tomonoriyamazaki/toytalk/web/tanuki_idle.png

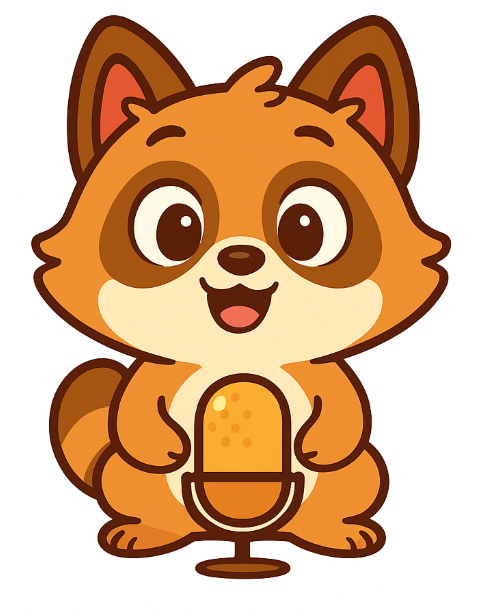
web/tanuki_idle.png
