tomonoriyamazaki/toytalk/devices/KiCad/OPL_Kicad_Library-master/OPL_Kicad_Library-master/Seeed Studio Wio SX1262 for XIAO nRF52840 v1.3/Wio-SX1262 for XIAO nRF52840.kicad_pcb

## KiCad design devices/KiCad/OPL_Kicad_Library-master/OPL_Kicad_Library-master/Seeed Studio Wio SX1262 for XIAO nRF52840 v1.3/Wio-SX1262 for XIAO nRF52840.kicad_pcb (2026-01-03)


Parts:
C1: 100nF; C0402; Voltage Rating 16V,X7R; MPN CC0402KRX7R7BB104
J1, J2: Header 1x7 2.54mm; H7-2.54; Part Type Header
K1: TS-1188E 6C81; SW4-SMD-7.0X3.5X3.5MM-90D; MPN TS-1188E 6C81; not fitted
R1: 10K; R0402; Power Rating 5%; MPN RC0402JR-0710KL
R2: 10K; R0402; Power Rating 5%; MPN RC0402JR-0710KL; not fitted
R3, R4, R5, R6: 22R; R0402; Power Rating 1%; MPN RC0402FR-0722RL
U1: Wio-SX1262; MODULE12P-1.27-11X11.6MM; MPN Wio-SX1262

Connections:
+3V3: C1.1, J2.3, R1.2, R2.2, U1.8 (VCC)
/D0: J1.1, K1.2, R2.1
/LORA_BUSY: J1.4, U1.11 (BUSY)
/LORA_DIO1: J1.2, U1.12 (DIO1)
/LORA_RF_SW1: J1.6, U1.1 (RF_SW1)
/LORA_RST: J1.3, R1.1, U1.5 (RST)
/LORA_SPI_MISO: J2.5, R4.1
/LORA_SPI_MOSI: J2.4, R5.1
/LORA_SPI_NSS: J1.5, R3.1
/LORA_SPI_SCK: J2.6, R6.1
GND: C1.2, J2.2, K1.1, K1.3 (S1), K1.4 (S2), U1.7 (GND1), U1.10 (GND2)
unnamed: R4.2, U1.2 (MISO)
unnamed: R5.2, U1.3 (MOSI)
unnamed: R3.2, U1.6 (NSS)
unnamed: R6.2, U1.4 (SCK)
VIN: J2.1


Board: 2 copper layers, 17.8 x 21.4 mm, 11 parts (0 on the bottom side), 15 nets.
