tomonoriyamazaki/toytalk/devices/mcu/esp32_s3/audio_speaker_tts_3/audio_speaker_tts_3.ino

#include <WiFi.h>
#include <WiFiClientSecure.h>
#include <driver/i2s.h>
#include "mbedtls/base64.h"

// ==== WiFi ====
const char* WIFI_SSID = "Buffalo-G-5830";
const char* WIFI_PASS = "sh6s3kagpp48s";

// ==== Lambda ====
const char* LAMBDA_HOST = "hbik6fueesqaftzkehtbwrr2ra0ucusi.lambda-url.ap-northeast-1.on.aws";
const char* LAMBDA_PATH = "/";

// ==== I2S PIN ====
#define PIN_BCLK   4
#define PIN_LRC    3
#define PIN_DOUT   5
#define PIN_AMP_SD 6

// ===== 追加: 受信状態 =====
String curEvent = "";
int curId = -1;
String curB64 = "";
bool inTtsJson = false;

// ===== mono → stereo 変換（音量調整付き） =====
void monoToStereo(int16_t* mono, int16_t* stereo, size_t samples) {
  const float VOLUME = 0.3;  // 30%に減衰（0.0-1.0）GAINピン未接続対策

  for (size_t i = 0; i < samples; i++) {
    int16_t sample = (int16_t)(mono[i] * VOLUME);
    stereo[2*i]     = sample;
    stereo[2*i + 1] = sample;
  }
}

// ===== 追加: イベント終了処理 =====
void handleEventEnd() {
  if (curEvent == "tts" && curId >= 0 && curB64.length() > 0) {
    Serial.println("===== COMPLETE PCM =====");
    Serial.printf("id=%d, b64_len=%d\n", curId, curB64.length());

    // Base64デコード（PSRAMを使用）
    size_t out_len = 0;
    int maxOut = curB64.length();
    uint8_t* mono_pcm = (uint8_t*)ps_malloc(maxOut);  // malloc → ps_malloc

    if (!mono_pcm) {
      Serial.println("[ERR] ps_malloc failed");
      curEvent = "";
      curId = -1;
      curB64 = "";
      inTtsJson = false;
      return;
    }

    int ret = mbedtls_base64_decode(
      mono_pcm, maxOut, &out_len,
      (const unsigned char*)curB64.c_str(),
      curB64.length()
    );

    Serial.printf("[DECODE] ret=%d, out_len=%d\n", ret, out_len);

    if (ret != 0 || out_len == 0) {
      Serial.println("[ERR] decode failed");
      free(mono_pcm);
      curEvent = "";
      curId = -1;
      curB64 = "";
      inTtsJson = false;
      return;
    }

    // mono → stereo 変換（PSRAMを使用）
    size_t samples = out_len / 2;
    size_t stereo_bytes = samples * 4;
    int16_t* stereo = (int16_t*)ps_malloc(stereo_bytes);  // malloc → ps_malloc

    if (!stereo) {
      Serial.println("[ERR] stereo ps_malloc failed");
      free(mono_pcm);
      curEvent = "";
      curId = -1;
      curB64 = "";
      inTtsJson = false;
      return;
    }

    monoToStereo((int16_t*)mono_pcm, stereo, samples);

    // I2S 再生
    size_t written = 0;
    i2s_write(I2S_NUM_1, stereo, stereo_bytes, &written, portMAX_DELAY);
    Serial.printf("[I2S] written=%d bytes\n", written);

    free(stereo);
    free(mono_pcm);
    Serial.println("========================");
  }

  curEvent = "";
  curId = -1;
  curB64 = "";
  inTtsJson = false;
}


// ===== 追加: 行ごとの処理 =====
void processLine(String line) {
  line.trim();

  // ---- chunk-size(hex) 行スキップ ----
  bool isHex = true;
  if (line.length() > 0) {
    for (int i = 0; i < line.length(); i++) {
      if (!isxdigit(line[i])) { isHex = false; break; }
    }
  }
  if (isHex && line.length() <= 4) {
    return;
  }

  // ---- event: ----
  if (line.startsWith("event:")) {
    // handleEventEnd();   // ← ①削除（ここだけ変更）
    curEvent = line.substring(6);
    curEvent.trim();
    return;
  }

  // ---- data: 最初の JSON ----
  if (line.startsWith("data:")) {
    String d = line.substring(5);
    d.trim();

    if (curEvent == "tts" && d.startsWith("{")) {
      // id
      int p = d.indexOf("\"id\":");
      if (p >= 0) {
        p += 5;
        int e = p;
        while (e < d.length() && isdigit(d[e])) e++;
        curId = d.substring(p, e).toInt();
      }

      // b64（途中のため " が無い場合あり）
      int b = d.indexOf("\"b64\":\"");
      if (b >= 0) {
        b += 7;
        String part = d.substring(b);
        part.replace("\"", "");
        curB64 += part;
      }

      inTtsJson = true;
    }
    return;
  }

  // ---- TTS JSON の途中チャンク ----
  if (curEvent == "tts" && inTtsJson) {

    // 終端 "}" チェック
    if (line.endsWith("\"}")) {
      String tmp = line;
      tmp.replace("\"}", "");
      curB64 += tmp;
      handleEventEnd();
      return;
    }

    // base64 続き
    curB64 += line;
    return;
  }

  // 他の行は無視
}


// ==== Lambda に固定メッセージ送って SSE を処理 ====
void sendSimpleSSE(const String& text)
{
  Serial.println("🚀 Sending to Lambda: " + text);

  WiFiClientSecure client;
  client.setInsecure();

  if (!client.connect(LAMBDA_HOST, 443)) {
    Serial.println("❌ connect failed");
    return;
  }

  // 送信ペイロード
  String payload =
    "{\"model\":\"OpenAI\",\"voice\":\"nova\","
    "\"messages\":[{\"role\":\"user\",\"content\":\"" + text + "\"}]}";

  // HTTPリクエスト
  String req =
    String("POST ") + LAMBDA_PATH + " HTTP/1.1\r\n"
    "Host: " + LAMBDA_HOST + "\r\n"
    "Content-Type: application/json\r\n"
    "Accept: text/event-stream\r\n"
    "Connection: close\r\n"
    "Content-Length: " + payload.length() + "\r\n\r\n"
    + payload;

  client.print(req);

  Serial.println("📡 Waiting SSE header...");

  // ---- HTTPヘッダ飛ばす ----
  while (true) {
    String line = client.readStringUntil('\n');
    if (line.length() == 0 || line == "\r") break;
  }

  Serial.println("📨 SSE START --------------------------------");

  // ---- SSEボディ ----
  while (client.connected() || client.available()) {
    if (client.available()) {
      String line = client.readStringUntil('\n');
      Serial.print("[RAW] ");
      Serial.println(line);
      processLine(line);   // ★追加
    } else {
      delay(1);
    }
  }

  Serial.println("🏁 SSE END ----------------------------------");

  handleEventEnd();  // 念のため
}

// ==== I2S セットアップ ====
void setupI2S() {
  pinMode(PIN_AMP_SD, OUTPUT);
  digitalWrite(PIN_AMP_SD, HIGH);

  i2s_config_t cfg = {
    .mode = (i2s_mode_t)(I2S_MODE_MASTER | I2S_MODE_TX),
    .sample_rate = 24000,
    .bits_per_sample = I2S_BITS_PER_SAMPLE_16BIT,
    .channel_format = I2S_CHANNEL_FMT_RIGHT_LEFT,
    .communication_format = (i2s_comm_format_t)(I2S_COMM_FORMAT_I2S | I2S_COMM_FORMAT_I2S_MSB),
    .intr_alloc_flags = 0,
    .dma_buf_count = 8,
    .dma_buf_len = 1024,
    .use_apll = true,
    .tx_desc_auto_clear = true,
    .fixed_mclk = 0
  };

  i2s_pin_config_t pins = {
    .bck_io_num = PIN_BCLK,
    .ws_io_num = PIN_LRC,
    .data_out_num = PIN_DOUT,
    .data_in_num = I2S_PIN_NO_CHANGE
  };

  i2s_driver_install(I2S_NUM_1, &cfg, 0, NULL);
  i2s_set_pin(I2S_NUM_1, &pins);
  i2s_set_clk(I2S_NUM_1, 24000, I2S_BITS_PER_SAMPLE_16BIT, I2S_CHANNEL_STEREO);
}

void setup() {
  Serial.begin(921600);
  delay(200);

  Serial.println("🚀 ToyTalk ESP32 Audio Player with Chunk Decoding");

  setupI2S();

  WiFi.mode(WIFI_STA);
  WiFi.begin(WIFI_SSID, WIFI_PASS);
  while (WiFi.status() != WL_CONNECTED) {
    delay(400);
    Serial.print(".");
  }
  Serial.printf("\n✅ WiFi connected: %s\n", WiFi.localIP().toString().c_str());

  // ---- テスト送信 ----
  sendSimpleSSE("こんにちは。テストです");
}

void loop() {
}
