tomonoriyamazaki/toytalk/devices/mcu/esp32_s3/toytalk_demo_v1.3_se_experimental/se_input_end.h

#pragma once

// Sound effect: input end (24kHz, 16bit, mono)
// Size: 61978 bytes

const unsigned char SE_INPUT_END[] PROGMEM = {
  0xcf, 0xff, 0xab, 0xff, 0xa9, 0xff, 0xb5, 0xff, 0xc3, 0xff, 0xda, 0xff, 0xf5, 0xff, 0x17, 0x00,
  0x3c, 0x00, 0x67, 0x00, 0x94, 0x00, 0xc7, 0x00, 0xfa, 0x00, 0x2e, 0x01, 0x64, 0x01, 0x96, 0x01,
  0xc3, 0x01, 0xee, 0x01, 0x13, 0x02, 0x31, 0x02, 0x49, 0x02, 0x5b, 0x02, 0x63, 0x02, 0x64, 0x02,
  0x5a, 0x02, 0x48, 0x02, 0x2f, 0x02, 0x0b, 0x02, 0xe0, 0x01, 0xac, 0x01, 0x70, 0x01, 0x2c, 0x01,
  0xdf, 0x00, 0x8d, 0x00, 0x36, 0x00, 0xda, 0xff, 0x7b, 0xff, 0x1b, 0xff, 0xb9, 0xfe, 0x59, 0xfe,
  0xfd, 0xfd, 0xa6, 0xfd, 0x55, 0xfd, 0x0e, 0xfd, 0xd3, 0xfc, 0xa3, 0xfc, 0x80, 0xfc, 0x6b, 0xfc,
  0x62, 0xfc, 0x69, 0xfc, 0x7f, 0xfc, 0xa2, 0xfc, 0xd5, 0xfc, 0x17, 0xfd, 0x66, 0xfd, 0xc0, 0xfd,
  0x25, 0xfe, 0x95, 0xfe, 0x0d, 0xff, 0x8d, 0xff, 0x12, 0x00, 0x9c, 0x00, 0x2a, 0x01, 0xb8, 0x01,
  0x45, 0x02, 0xcf, 0x02, 0x53, 0x03, 0xce, 0x03, 0x40, 0x04, 0xa6, 0x04, 0xfe, 0x04, 0x45, 0x05,
  0x7b, 0x05, 0x9e, 0x05, 0xaa, 0x05, 0xa0, 0x05, 0x81, 0x05, 0x4a, 0x05, 0xfe, 0x04, 0x9f, 0x04,
  0x2a, 0x04, 0xa4, 0x03, 0x0d, 0x03, 0x66, 0x02, 0xb1, 0x01, 0xf2, 0x00, 0x2b, 0x00, 0x5d, 0xff,
  0x8e, 0xfe, 0xbe, 0xfd, 0xee, 0xfc, 0x23, 0xfc, 0x5e, 0xfb, 0xa0, 0xfa, 0xef, 0xf9, 0x4b, 0xf9,
  0xb7, 0xf8, 0x38, 0xf8, 0xce, 0xf7, 0x7a, 0xf7, 0x40, 0xf7, 0x21, 0xf7, 0x1b, 0xf7, 0x34, 0xf7,
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
  0x54, 0x0d, 0x99, 0x11, 0xb6, 0x15, 0xa2, 0x19, 0x54, 0x1d, 0xc2, 0x20, 0xe1, 0x23, 0xac, 0x26,
  0x1b, 0x29, 0x26, 0x2b, 0xc7, 0x2c, 0xfa, 0x2d, 0xba, 0x2e, 0x05, 0x2f, 0xd8, 0x2e, 0x34, 0x2e,
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
};
const unsigned int SE_INPUT_END_LEN = 61978;
