tomonoriyamazaki/toytalk/devices/mcu/esp32_s3/audio_speaker_test_base64_openai_pcm/raw_pcm_test_1s.h

unsigned char c__Users_exodj_Documents_Audacity_raw_pcm_test_1s_pcm[] = {
  0x0E, 0x00, 0x0F, 0x00, 0x04, 0x00, 0x13, 0x00, 0x02, 0x00, 0x13, 0x00, 0x09, 0x00, 0x0B, 0x00, 
0x11, 0x00, 0x0C, 0x00, 0x14, 0x00, 0x04, 0x00, 0x0A, 0x00, 0x01, 0x00, 0x09, 0x00, 0x07, 0x00, 
0x0B, 0x00, 0x04, 0x00, 0x05, 0x00, 0x0A, 0x00, 0x06, 0x00, 0x09, 0x00, 0x00, 0x00, 0x08, 0x00, 
0x01, 0x00, 0x09, 0x00, 0x00, 0x00, 0x04, 0x00, 0xFF, 0xFF, 0x01, 0x00, 0x00, 0x00, 0xFC, 0xFF, 
0x00, 0x00, 0xFD, 0xFF, 0xFD, 0xFF, 0xF8, 0xFF, 0xFC, 0xFF, 0xF7, 0xFF, 0xFF, 0xFF, 0xF6, 0xFF, 
0x00, 0x00, 0xF5, 0xFF, 0xF7, 0xFF, 0xF7, 0xFF, 0xF4, 0xFF, 0xF9, 0xFF, 0xEC, 0xFF, 0xFB, 0xFF, 
0xEE, 0xFF, 0xF9, 0xFF, 0xEE, 0xFF, 0xF2, 0xFF, 0xEF, 0xFF, 0xED, 0xFF, 0xF2, 0xFF, 0xE8, 0xFF, 
0xF0, 0xFF, 0xED, 0xFF, 0xF3, 0xFF, 0xE8, 0xFF, 0xEE, 0xFF, 0xE2, 0xFF, 0xED, 0xFF, 0xE5, 0xFF, 
0xEE, 0xFF, 0xE6, 0xFF, 0xE6, 0xFF, 0xE9, 0xFF, 0xE1, 0xFF, 0xE8, 0xFF, 0xDC, 0xFF, 0xEE, 0xFF, 
0xDF, 0xFF, 0xF0, 0xFF, 0xE2, 0xFF, 0xE3, 0xFF, 0xE4, 0xFF, 0xE2, 0xFF, 0xEB, 0xFF, 0xDB, 0xFF, 
0xED, 0xFF, 0xDD, 0xFF, 0xE4, 0xFF, 0xE1, 0xFF, 0xDD, 0xFF, 0xE9, 0xFF, 0xD6, 0xFF, 0xEC, 0xFF, 
0xDA, 0xFF, 0xE5, 0xFF, 0xE1, 0xFF, 0xDB, 0xFF, 0xE7, 0xFF, 0xD3, 0xFF, 0xEA, 0xFF, 0xD7, 0xFF, 
0xE3, 0xFF, 0xD9, 0xFF, 0xD9, 0xFF, 0xE8, 0xFF, 0xD7, 0xFF, 0xE9, 0xFF, 0xD7, 0xFF, 0xE3, 0xFF, 
0xDB, 0xFF, 0xE6, 0xFF, 0xEA, 0xFF, 0xDC, 0xFF, 0xE7, 0xFF, 0xD7, 0xFF, 0xEA, 0xFF, 0xE5, 0xFF, 
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
0x13, 0x00, 0x16, 0x00, 0x12, 0x00, 0x11, 0x00, 0x0B, 0x00, 0x14, 0x00, 0x0B, 0x00, 0x0E, 0x00, 
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
};
unsigned int c__Users_exodj_Documents_Audacity_raw_pcm_test_1s_pcm_len = sizeof(c__Users_exodj_Documents_Audacity_raw_pcm_test_1s_pcm);
